CherryPichu/Arduino_Table_Clock/프로젝트/temp_humi.JPG

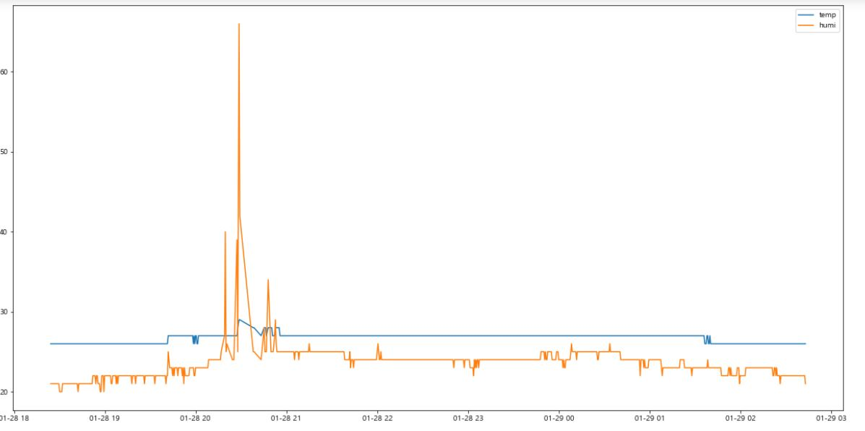
프로젝트/temp_humi.JPG
