CherryPichu/Arduino_Table_Clock/프로젝트/센서 모듈 케이스.JPG

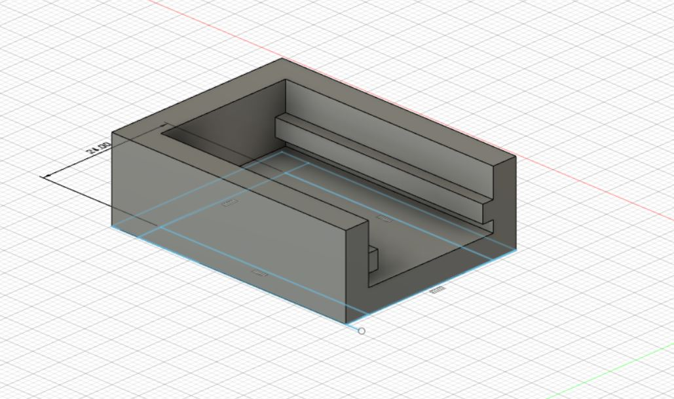
프로젝트/센서 모듈 케이스.JPG
