CherryPichu/Arduino_Table_Clock/프로젝트/습도 분석 _ 한림 메이커 스페이스.JPG

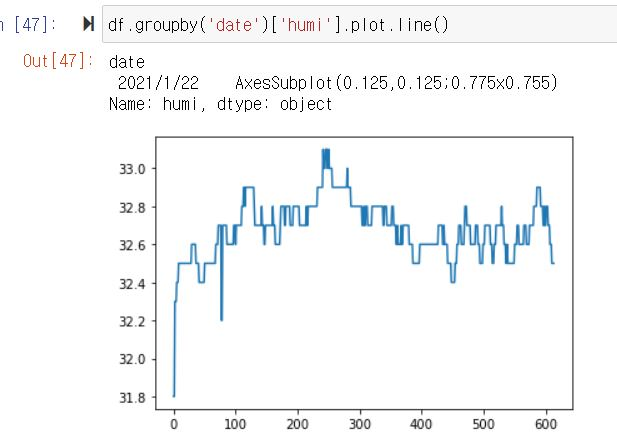
프로젝트/습도 분석 _ 한림 메이커 스페이스.JPG
