CherryPichu/Arduino_Table_Clock/프로젝트/아두이노 나노 센서 회로.jpg

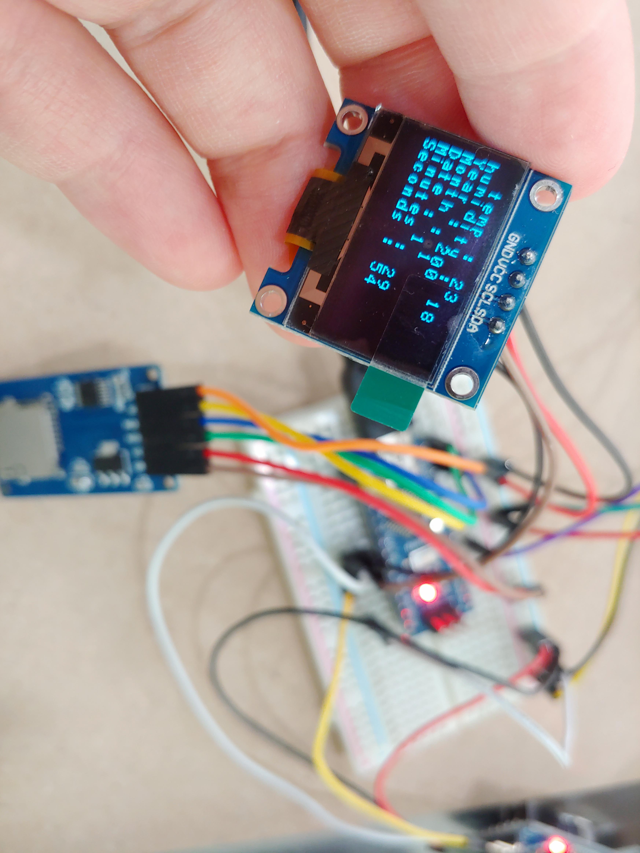
프로젝트/아두이노 나노 센서 회로.jpg
