CherryPichu/Arduino_Table_Clock/프로젝트/조도 데이터 02_02.JPG

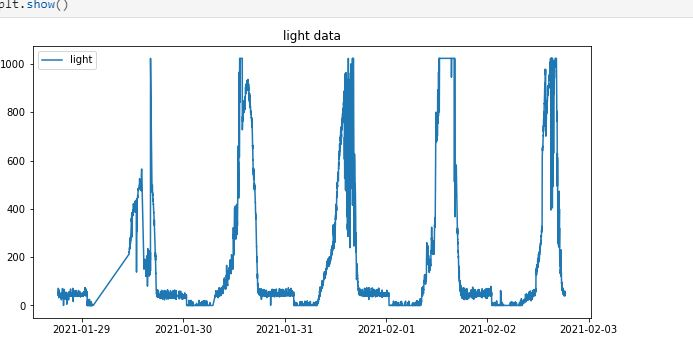
프로젝트/조도 데이터 02_02.JPG
