CherryPichu/Arduino_Table_Clock/프로젝트/허남정 탁상시계.JPG

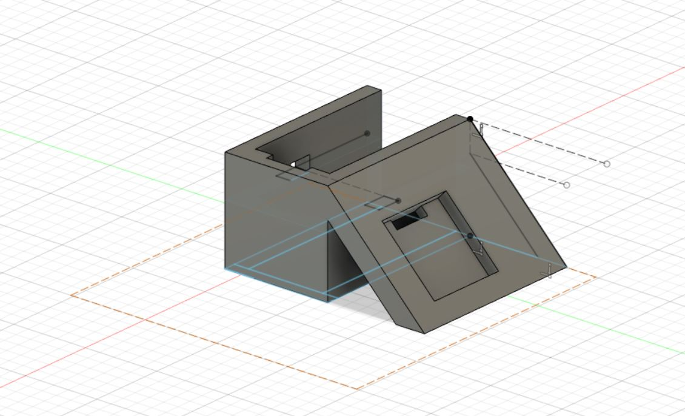
프로젝트/허남정 탁상시계.JPG
